samarjit/MyIMX233/parts/bom_template_2016-08-18.csv

Part/Designator | Manufacture Part Number/Seeed SKU | Quantity
C1 | RHA | 1
D1,D2 | CC0603KRX7R9BB102 | 2
