samarjit/MyIMX233/ReferenceSch/calculator.pdf

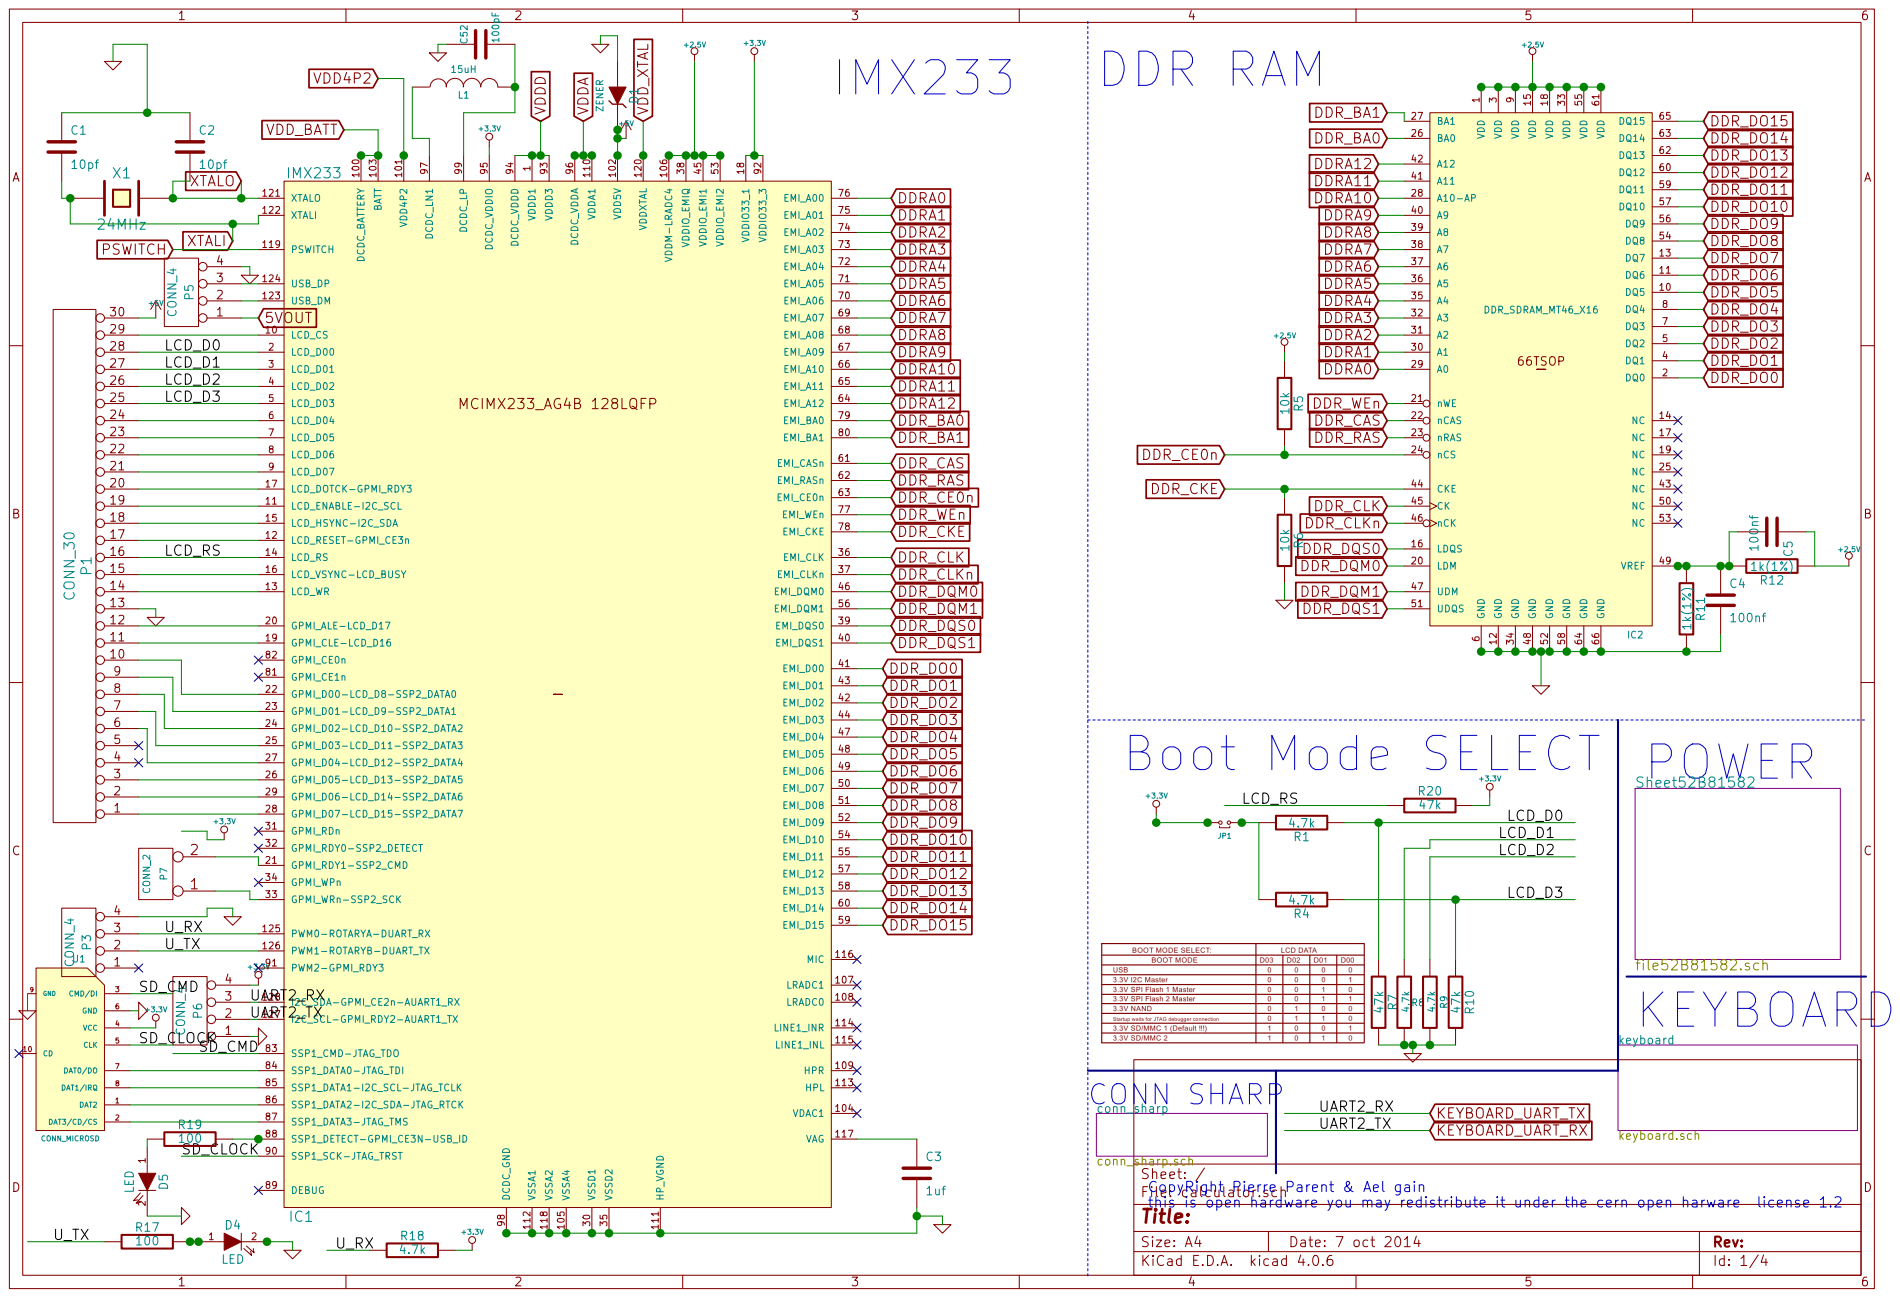
[picture p51: page 1]

66TSOP Schematic Symbol Drawn By Opendous Inc. www.opendous.org VDD

Schematic Symbol Drawn By Opendous Inc. www.opendous.org VDDD1

SSP1_SCK-JTAG_TRST 90

this is open hardware you may redistribute it under the cern open harware license 1.2 | Id: 1/4 Title: File: calculator.sch Sheet: /

CopyRight Pierre Parent & Ael gain

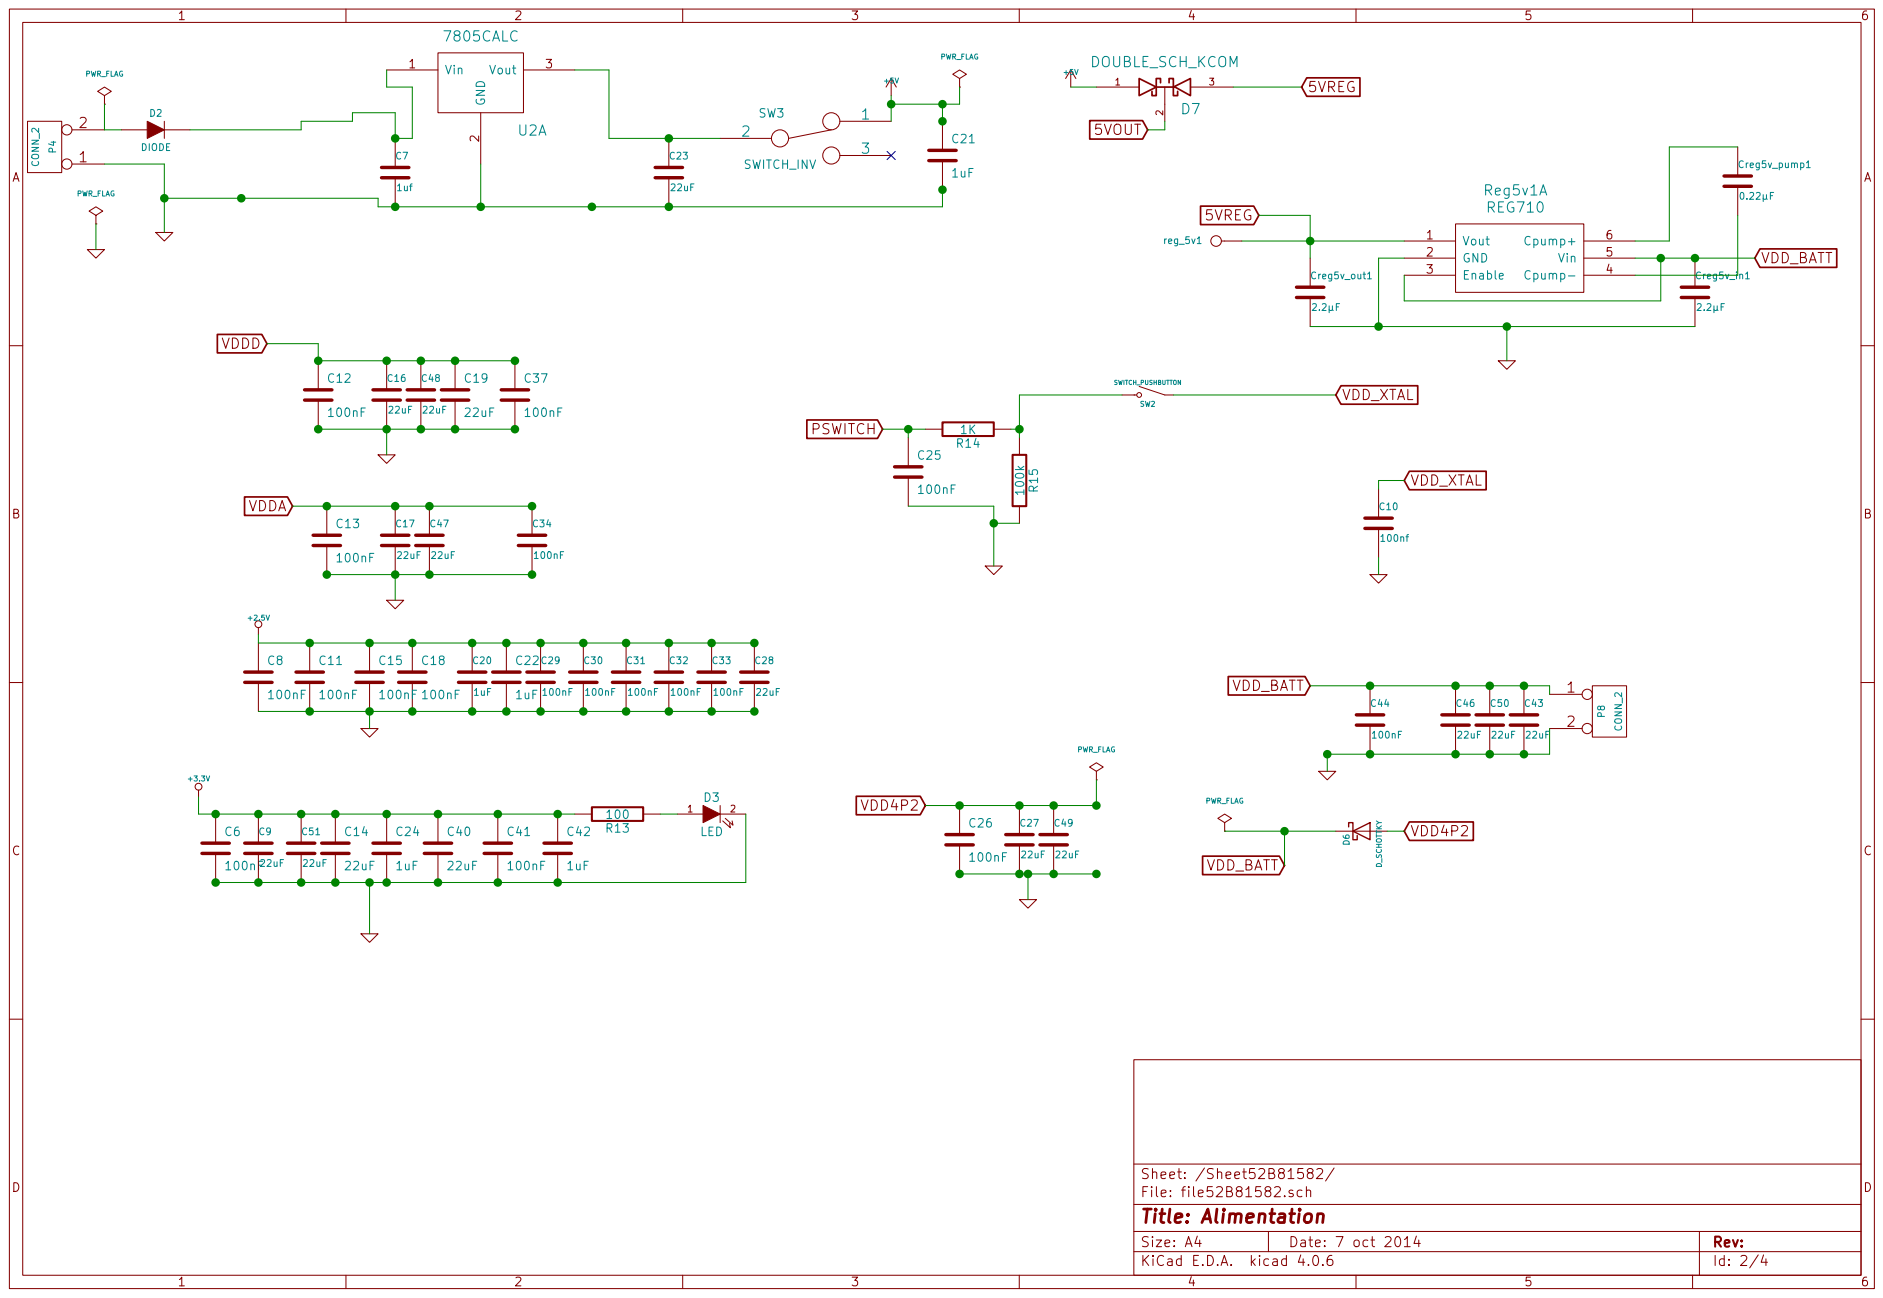
[picture p52: page 2]

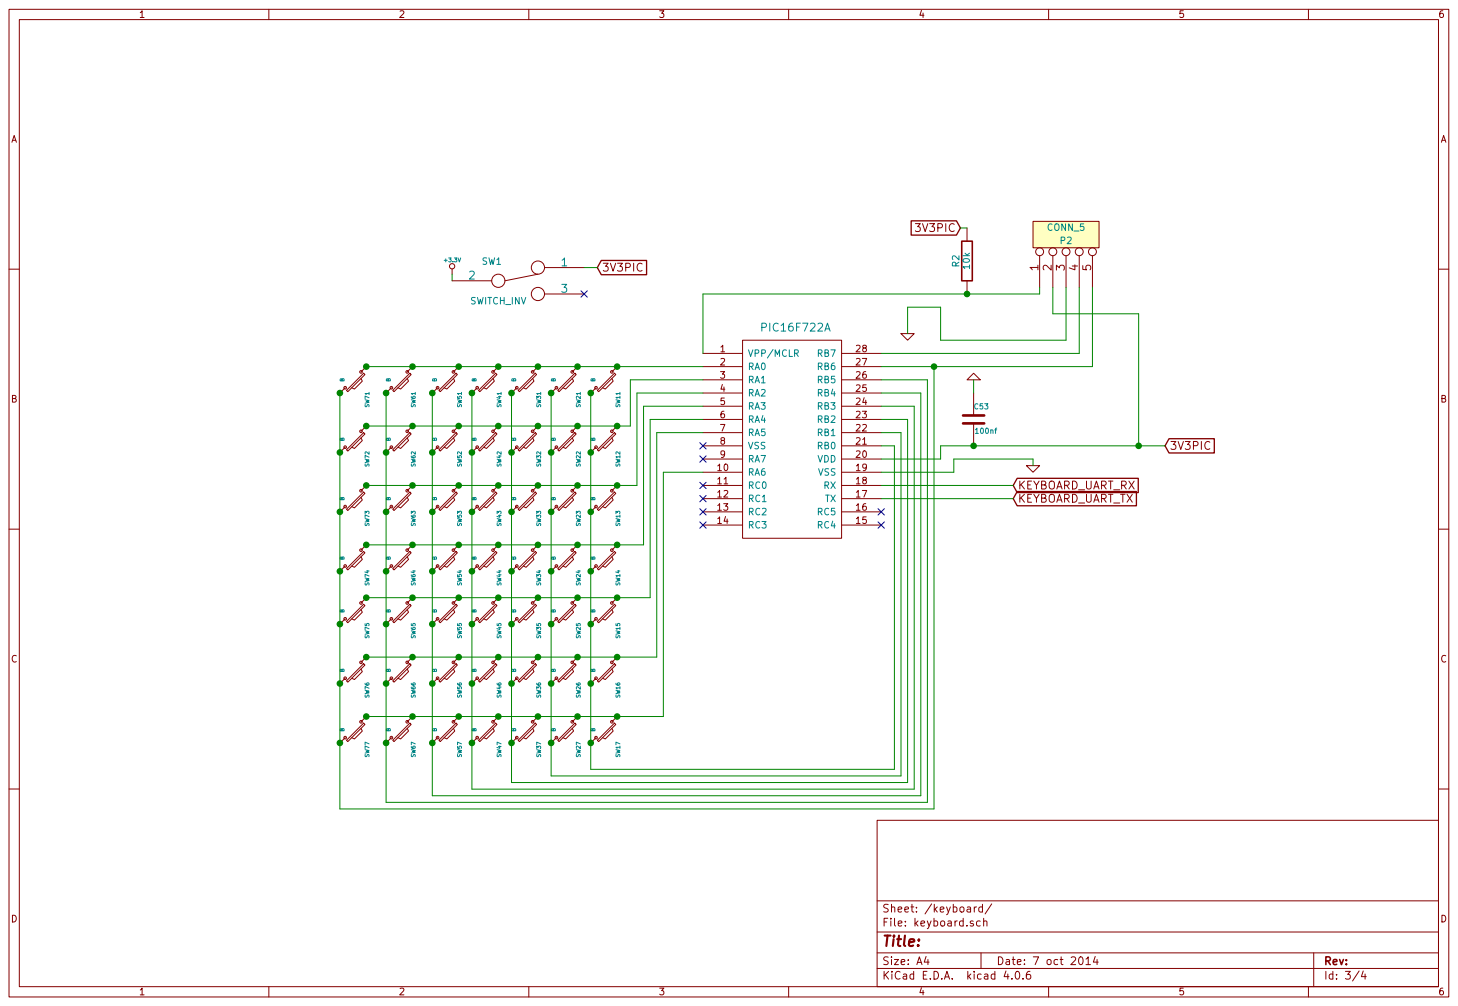
[picture p53: page 3]

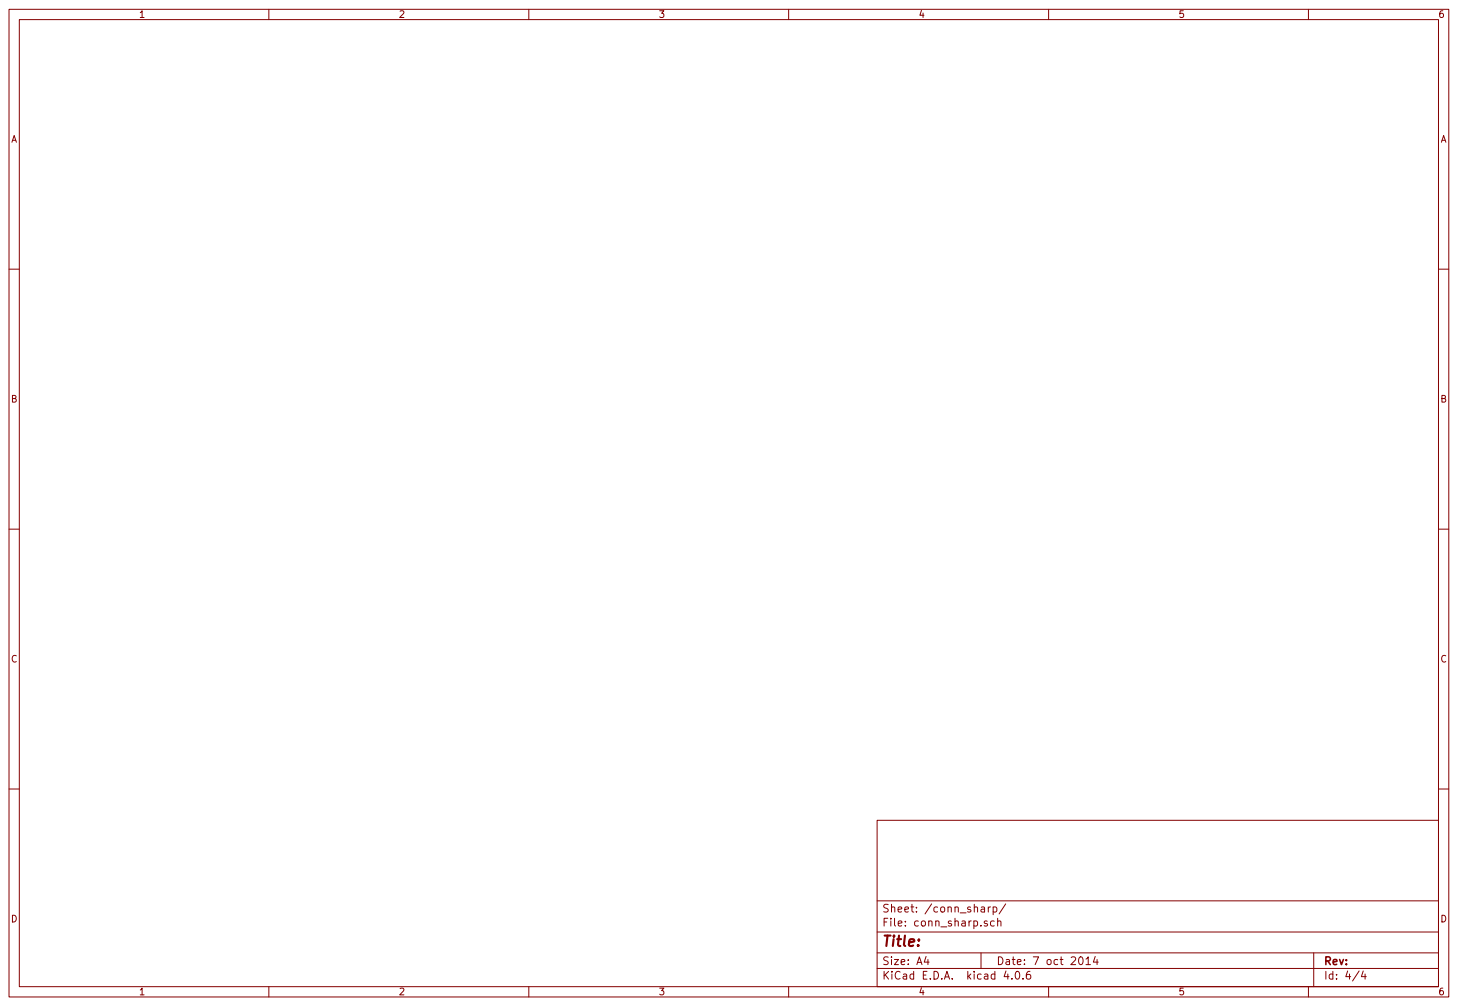
[picture p54: page 4]
