samarjit/MyIMX233/ReferenceSch/Clementine Core.PDF

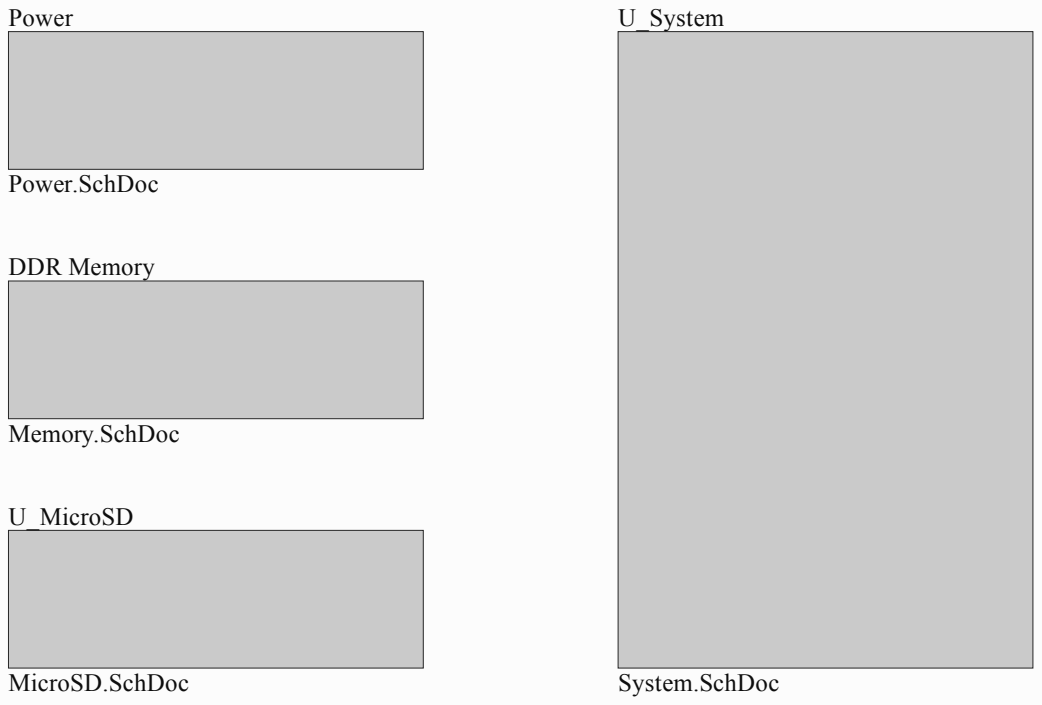
[picture p55: page 1]
DDR Memory

Clementi ne Cor e - T op L evel | 88-0511 Ja y C a rl s n N SE P.O . Bo x Li nc o ln, NE | B

Revision A1 | Pro ject: ne C ore.PrjPcb

6/16/2015 4:06:43 PM | Sheet 1 of 5

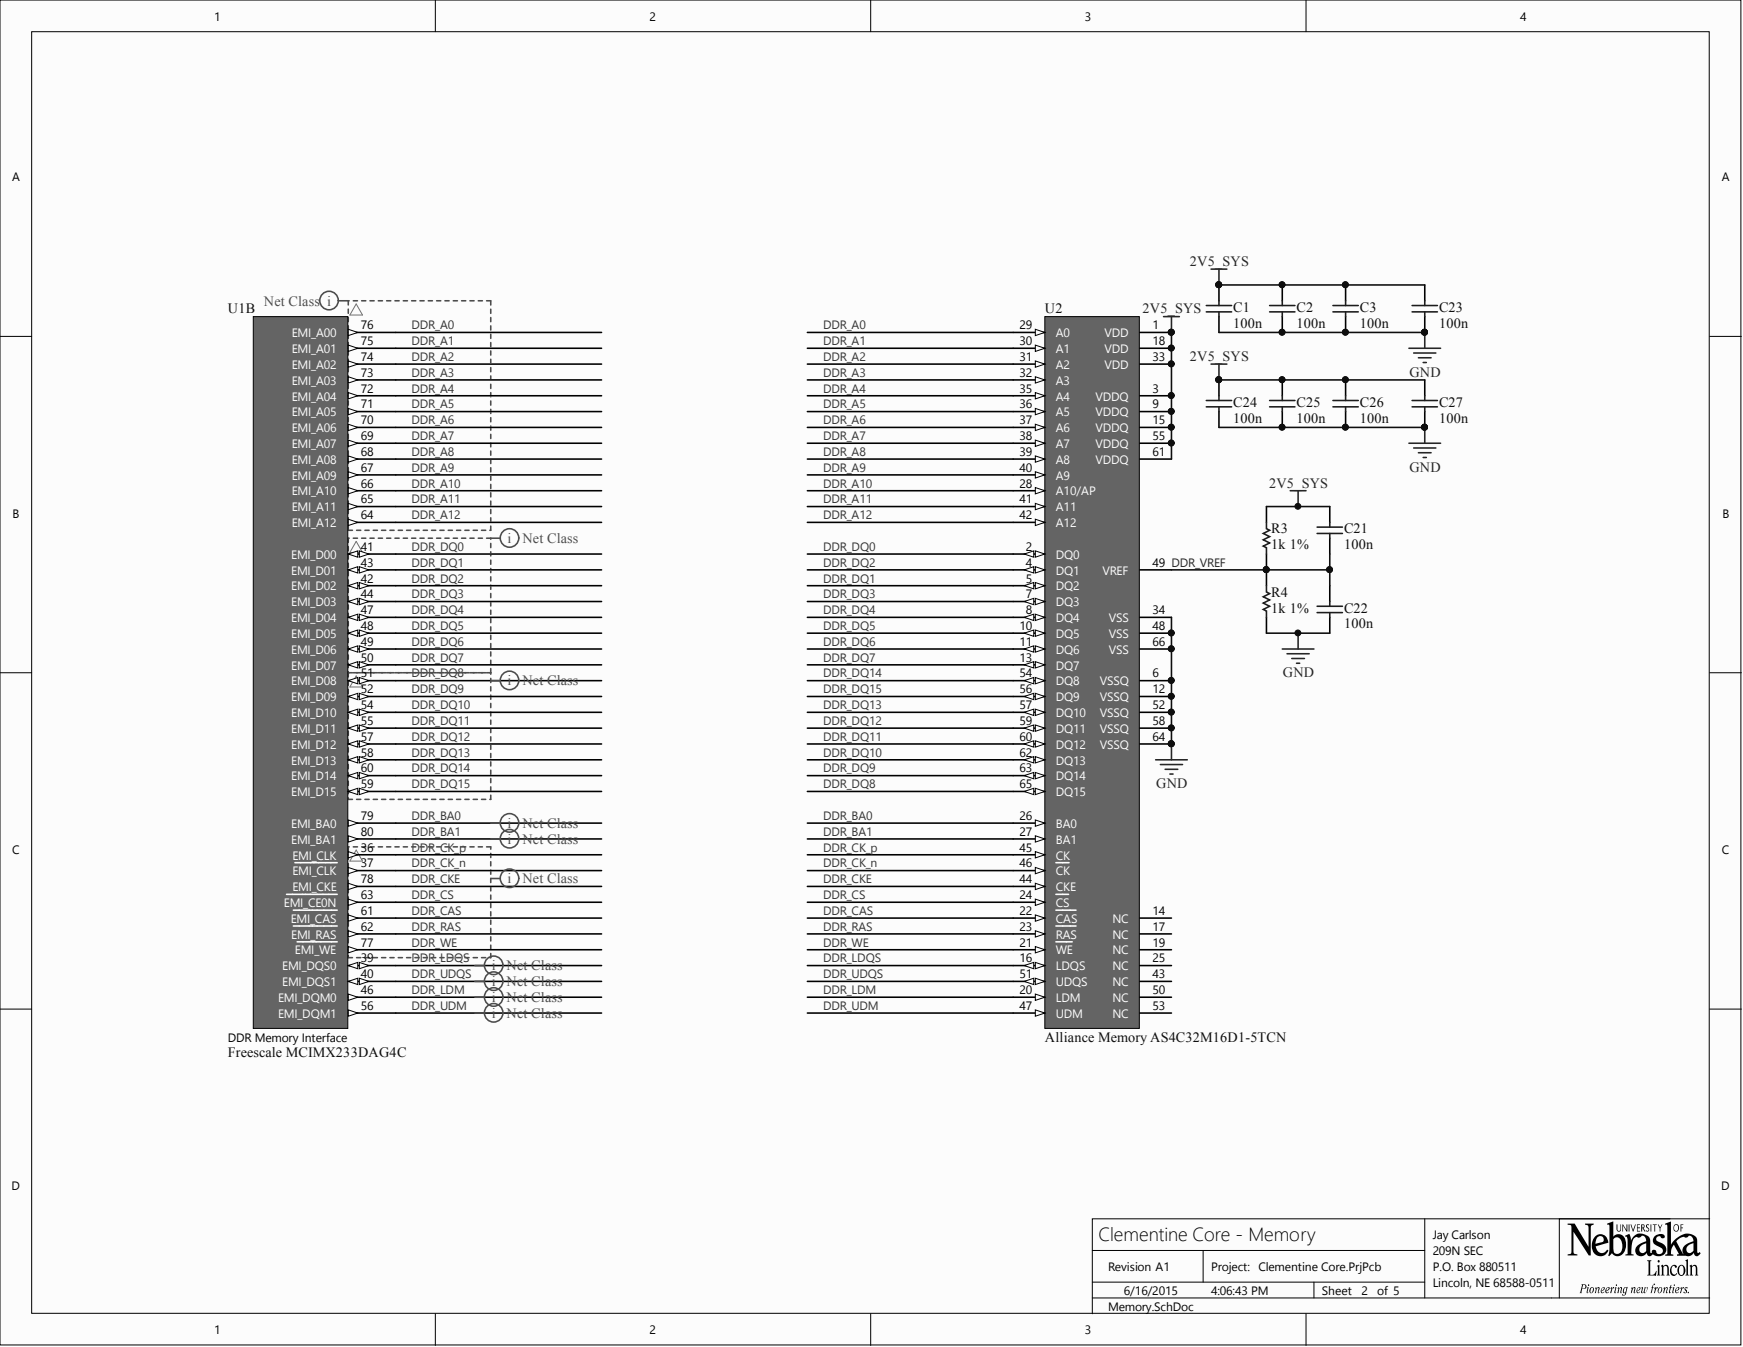
[picture p56: page 2]
Net Clas; Net Clas Net Clas; iance Memory; ory Interfa Freescale MCIMX

or | Ja2 y 9 N Co Boaln, rlxs NE Co8n8 Li0 8-0 | B

e - Mem ject: Clementi

Revi i

Sheet ore.PrjPc

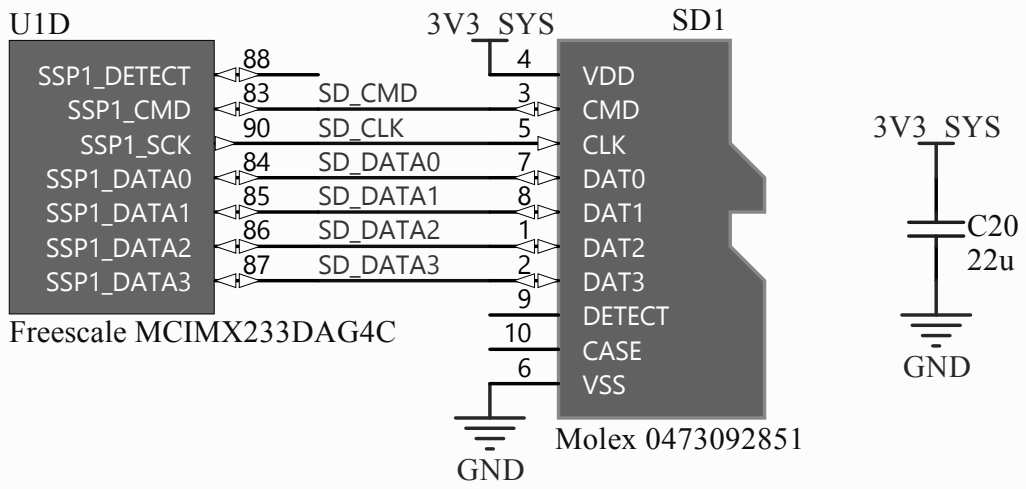
[picture p57: page 3]
Freescale MCIMX233DAG4C; DAT2 1 DAT3 2; CMD 3; VDD 4; CLK 5; VSS 6; DAT0 7 DAT1 8; DETECT 9 CASE 10; Molex 0473092851

e - Mi cr oSD | 88-0511 | B

ject: Cl em entine C

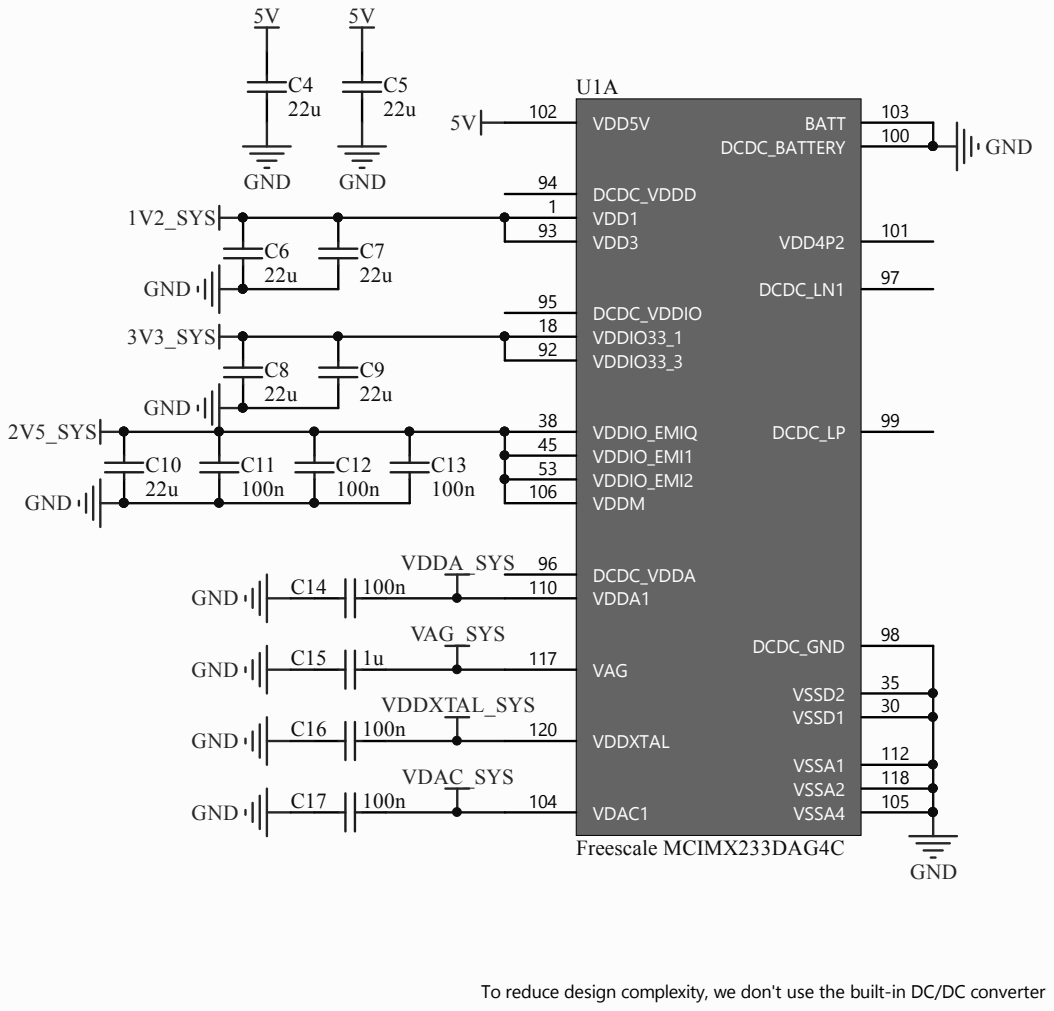
[picture p58: page 4]

VDDIO33_3 92

C10 C11 C12 C13 | VDDIO_EMI1 45

To reduce design complexity, we don't use the built-in DC/DC converter

ject: Clem entine C

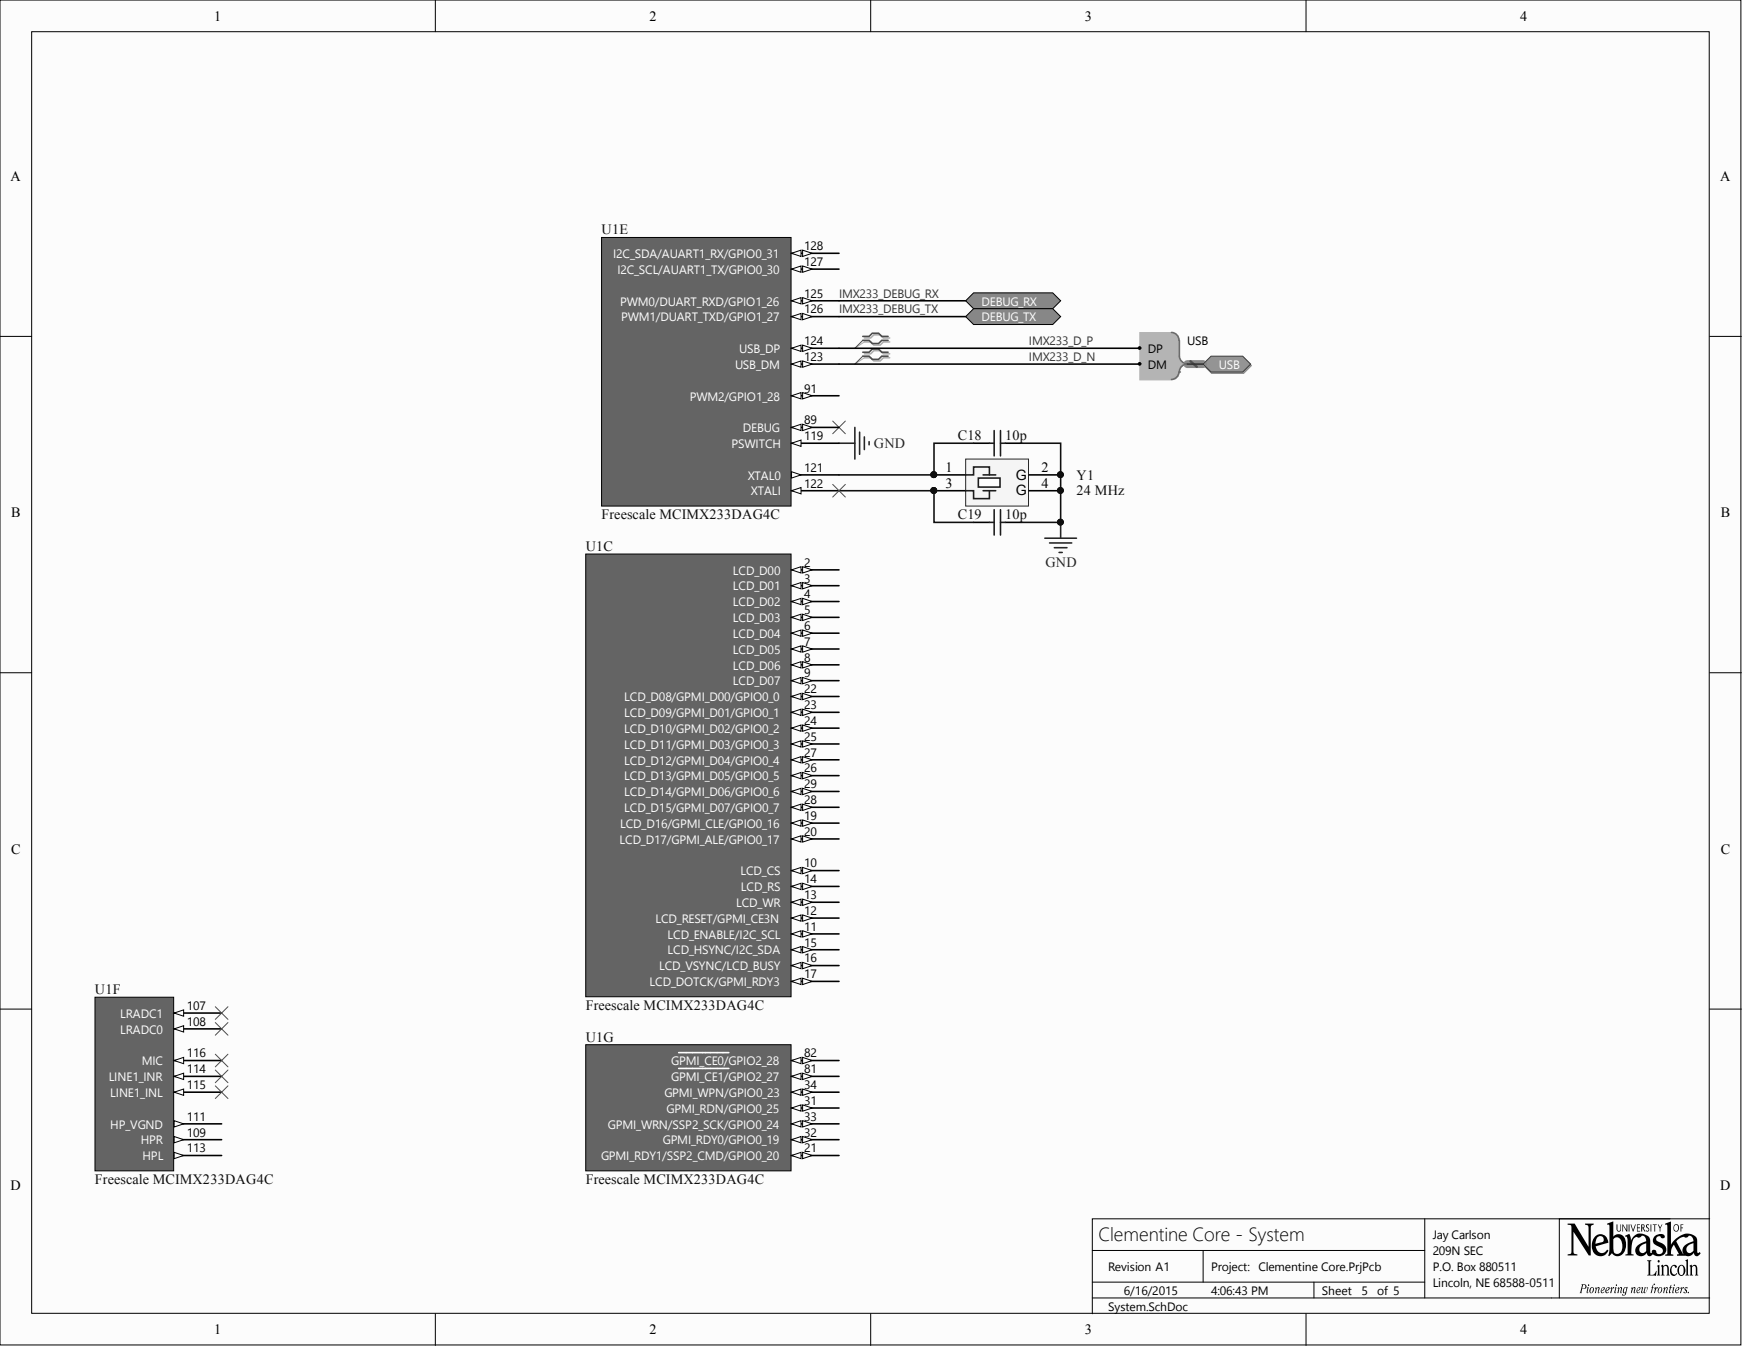
[picture p59: page 5]
24 MHz; LCD_ENABLE/I2C_SCL; 11 LCD_RESET/GPMI_CE3N; 12 LCD_WR; 13 LCD_RS; LCD_D13/GPMI_D05/GPIO0_5; 26 LCD_D12/GPMI_D04/GPIO0_4; LCD_D15/GPMI_D07/GPIO0_7; 28 LCD_D14/GPMI_D06/GPIO0_6; Freescale MCIMX233DAG4C; USB_DM; 123 USB_DP; I2C_SCL/AUART1_TX/GPIO0_30; 127 I2C_SDA/AUART1_RX/GPIO0_31; HPR; 109 HP_VGND; GPMI_RDY0/GPIO0_19; 32 GPMI_WRN/SSP2_SCK/GPIO0_24; GPMI_WPN/GPIO0_23; 34 GPMI_CE1/GPIO2_27; 81 GPMI_CE0/GPIO2_28

e - System | 88-0511 | B

ject: Clementine C

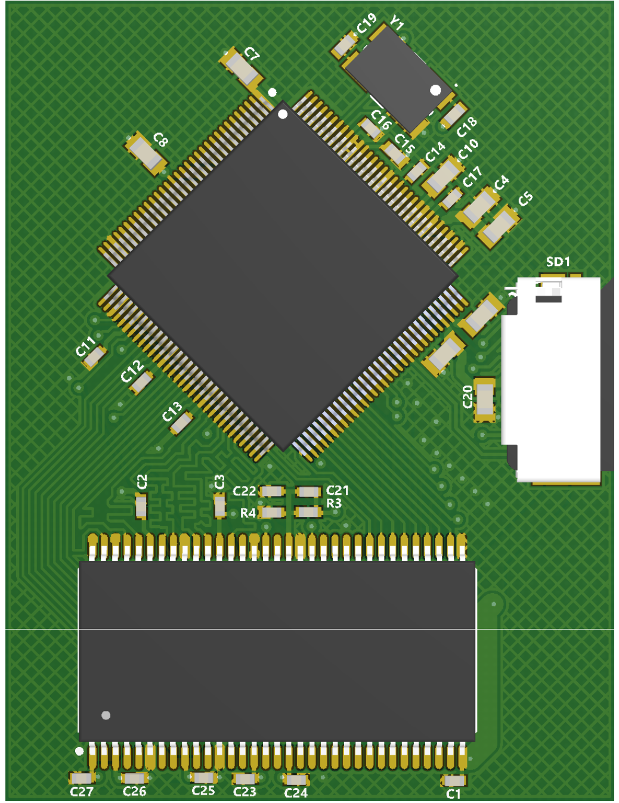
[picture p60: page 6]

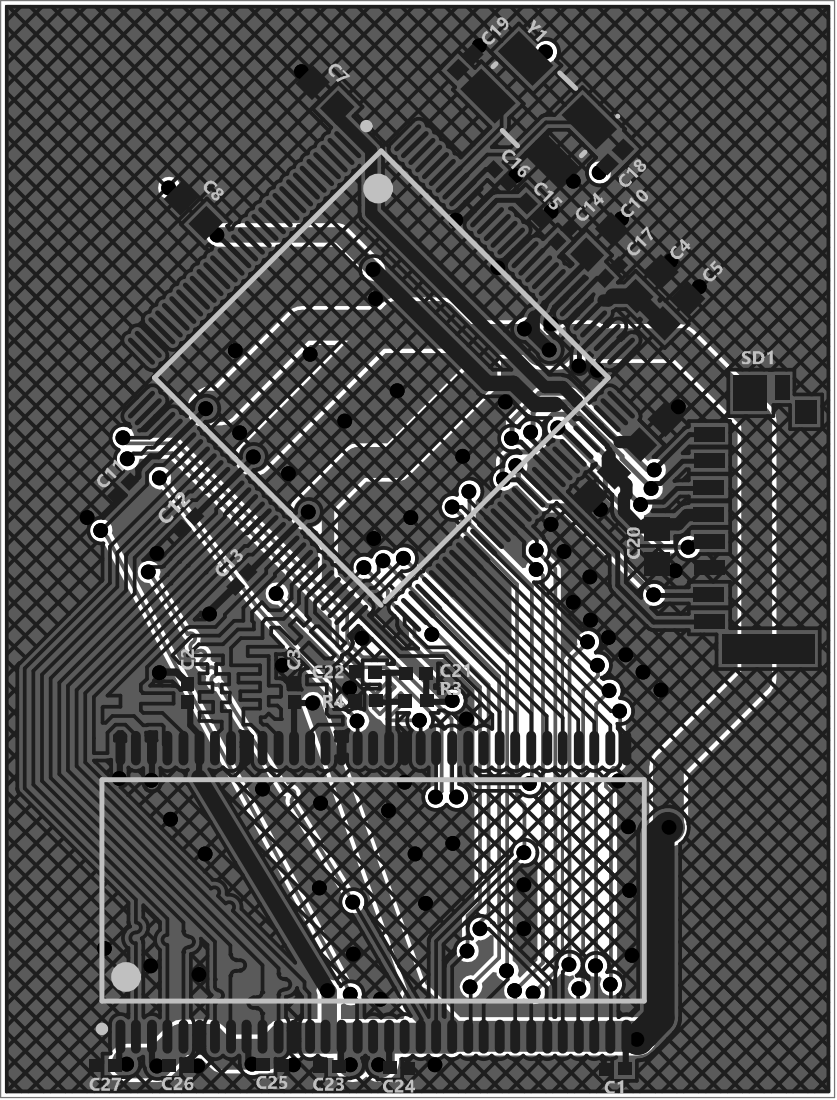
[picture p61: page 7]
