samarjit/MyIMX233/ReferenceSch/iMX233-OLinuXino-NANO_Rev_B.pdf

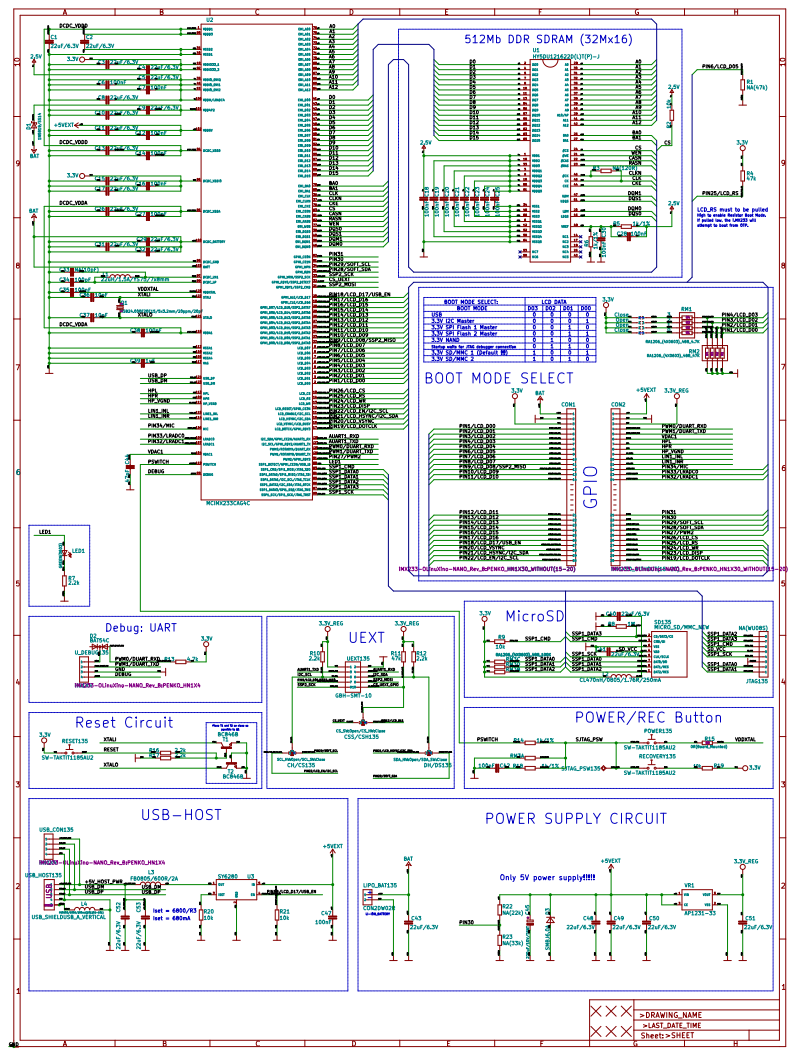
[picture p62: page 1]
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

attempt to boot from OTP. GPIO

3.3V I2C Master
3.3V SPI Flash 1 Master
3.3V SPI Flash 2 Master
3.3V NAND
Startup waits for JTAG debugger connection
3.3V SD/MMC 1 (Default !!!)

File: iMX233-OLinuXino-NANO_Rev_B.sch Sheet: / POWER SUPPLY CIRCUIT

Id: 1/1 Title: iMX233-OLinuXino-NANO_Rev_B.sch
